ArminRehberger/LED-Matrix-control-with-Teensy-4.0/KiCad/LEDMatrix.kicad_pcb

## KiCad design Esquema/Esquema.kicad_sch

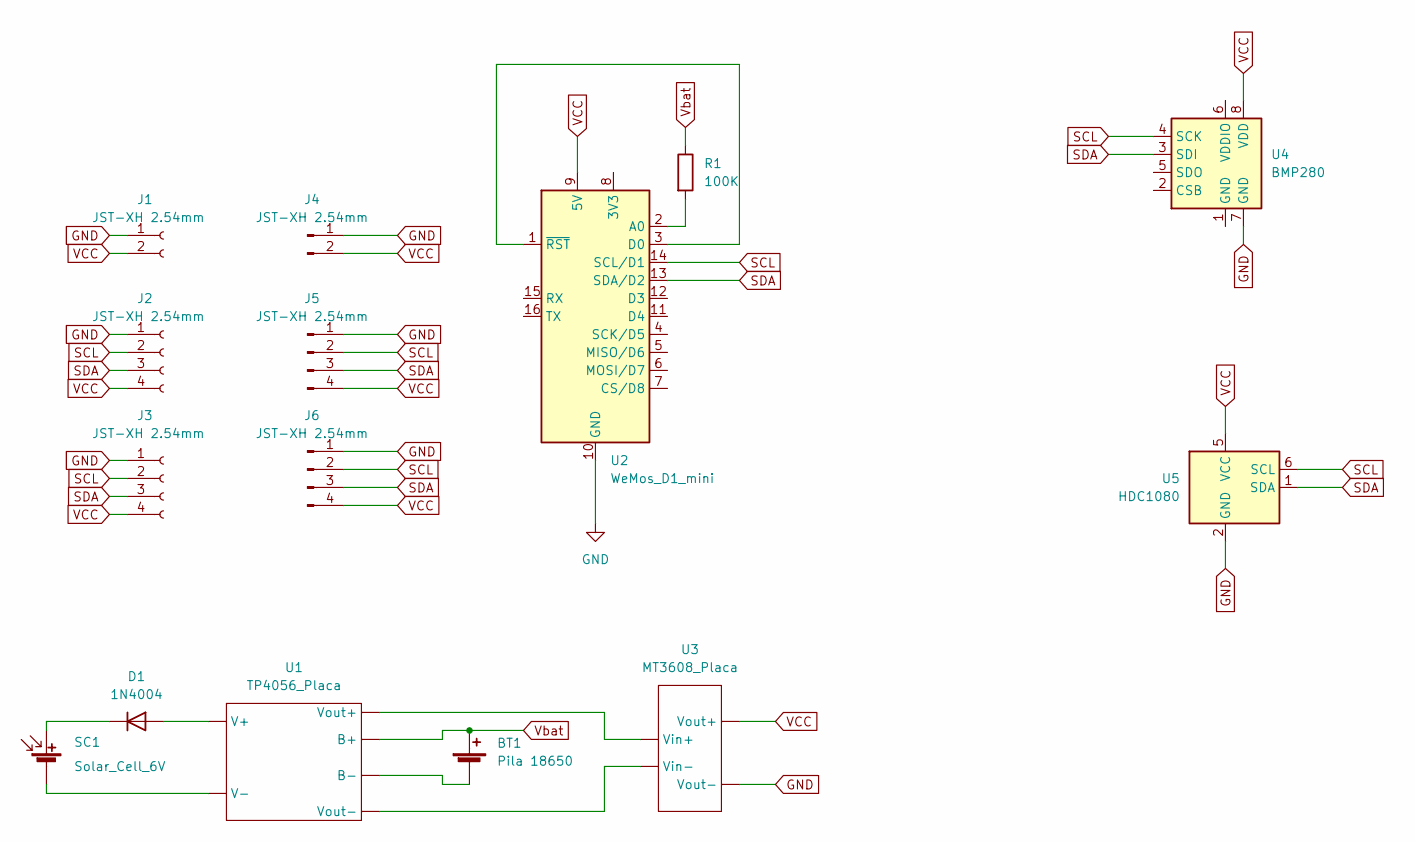
[picture p5: schematic Esquema.kicad_sch]

Parts:
BT1: Pila 18650
D1: 1N4004; D_DO-41_SOD81_P10.16mm_Horizontal
J1, J2, J3, J4, J5, J6: JST-XH 2.54mm
R1: 100K
SC1: Solar_Cell_6V
U1: TP4056_Placa
U2: WeMos_D1_mini; WEMOS_D1_mini_light
U3: MT3608_Placa
U4: BMP280; Bosch_LGA-8_2x2.5mm_P0.65mm_ClockwisePinNumbering
U5: HDC1080; Texas_PWSON-N6

Connections:
GND: J1.1, J2.1, J3.1, J4.1, J5.1, J6.1, U2.10 (GND), U3., U4.7 (GND), U5.2 (GND)
unnamed: BT1.2 (-), U1.
unnamed: D1.1 (K), SC1.1 (+)
unnamed: D1.2 (A), U1.
unnamed: R1.2, U2.2 (A0)
unnamed: SC1.2 (-), U1.
unnamed: U1., U3.
unnamed: U2.1 (~RST), U2.3 (D0)
SCL: J2.2, J3.2, J5.2, J6.2, U2.14 (SCL/D1), U4.4 (SCK), U5.6 (SCL)
SDA: J2.3, J3.3, J5.3, J6.3, U2.13 (SDA/D2), U4.3 (SDI), U5.1 (SDA)
VCC: J1.2, J2.4, J3.4, J4.2, J5.4, J6.4, U2.9 (5V), U3., U4.8 (VDD), U5.5 (VCC)
Vbat: BT1.1 (+), R1.1, U1.
